tsunghowu/insta360_ble_rc_rpi_pico_w/ble_simple_peripheral.py

# This example demonstrates a UART periperhal.

import bluetooth
import random
import struct
import time
from ble_advertising import advertising_payload

from micropython import const

_IRQ_CENTRAL_CONNECT = const(1)
_IRQ_CENTRAL_DISCONNECT = const(2)
_IRQ_GATTS_WRITE = const(3)

_FLAG_READ = const(0x0002)
_FLAG_WRITE_NO_RESPONSE = const(0x0004)
_FLAG_WRITE = const(0x0008)
_FLAG_NOTIFY = const(0x0010)

_UART_UUID = bluetooth.UUID("6E400001-B5A3-F393-E0A9-E50E24DCCA9E")
_UART_TX = (
    bluetooth.UUID("6E400003-B5A3-F393-E0A9-E50E24DCCA9E"),
    _FLAG_READ | _FLAG_NOTIFY,
)
_UART_RX = (
    bluetooth.UUID("6E400002-B5A3-F393-E0A9-E50E24DCCA9E"),
    _FLAG_WRITE | _FLAG_WRITE_NO_RESPONSE,
)
_UART_SERVICE = (
    _UART_UUID,
    (_UART_TX, _UART_RX),
)


class BLESimplePeripheral:
    def __init__(self, ble, name="Insta360 GPS Remote", _BLE_SERVICE=_UART_SERVICE, _BLE_SERVICE_UUID=_UART_UUID):
        self._ble = ble
        self._ble.active(True)
        self._ble.irq(self._irq)
        print(_BLE_SERVICE)
        #((self._handle_tx, self._handle_rx),) = self._ble.gatts_register_services((_UART_SERVICE,))
        # ( (hr,), (tx, rx,), )
        ((self._handle_tx, self._handle_rx, self._handle_misc),(_,_,_,_,_,_,_,_,_,), ) = self._ble.gatts_register_services(_BLE_SERVICE)
        
        self._ble.gatts_write(self._handle_tx, struct.pack("<B", 0x00))
        self._ble.gatts_write(self._handle_misc, struct.pack("<H", 0x0201))
        self._connections = set()
        self._write_callback = None
        self._payload = advertising_payload(name=name, services=[_BLE_SERVICE_UUID])
        self._advertise()

    def _irq(self, event, data):
        # Track connections so we can send notifications.
        if event == _IRQ_CENTRAL_CONNECT:
            conn_handle, _, _ = data
            print("New connection", conn_handle)
            self._connections.add(conn_handle)
        elif event == _IRQ_CENTRAL_DISCONNECT:
            conn_handle, _, _ = data
            print("Disconnected", conn_handle)
            self._connections.remove(conn_handle)
            # Start advertising again to allow a new connection.
            self._advertise()
        elif event == _IRQ_GATTS_WRITE:
            conn_handle, value_handle = data
            value = self._ble.gatts_read(value_handle)
            if value_handle == self._handle_rx and self._write_callback:
                self._write_callback(value)

    def send(self, data):
        for conn_handle in self._connections:
            self._ble.gatts_notify(conn_handle, self._handle_tx, data)

    def is_connected(self):
        if self._connections != None:
            return len(self._connections) > 0
        return False

    def _advertise(self, interval_us=500000):
        print("Starting advertising")
        #print(self._payload)
        self._ble.gap_advertise(interval_us, adv_data=self._payload)

    def on_write(self, callback):
        self._write_callback = callback

    def disconnect(self):
        for handle in self._connections:
            self._ble.gap_disconnect(handle)
        self._reset()

    def _reset(self):
        self._payload = None
        self._connections = None

def demo():
    ble = bluetooth.BLE()
    p = BLESimplePeripheral(ble)

    def on_rx(v):
        print("RX", v)

    p.on_write(on_rx)

    i = 0
    while True:
        if p.is_connected():
            # Short burst of queued notifications.
            for _ in range(3):
                data = str(i) + "_"
                print("TX", data)
                p.send(data)
                i += 1
        time.sleep_ms(100)


if __name__ == "__main__":
    demo()
